Tengyez/bcdwatch/docs/assembled-pcb.png

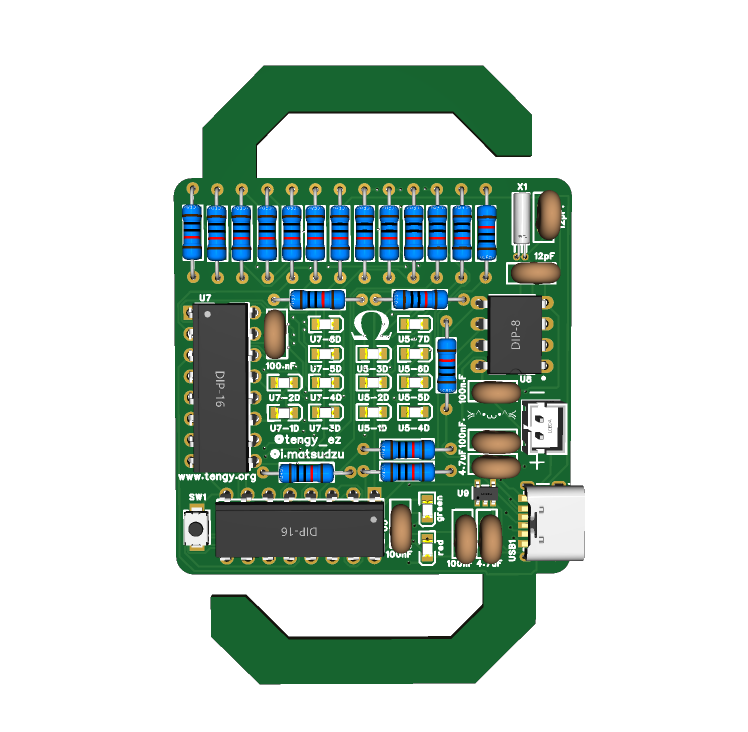
docs/assembled-pcb.png
