Tengyez/bcdwatch/docs/pcb-wiring.png

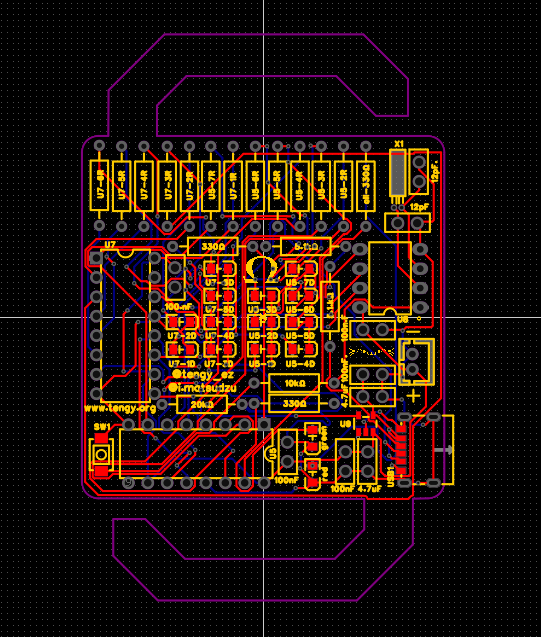
docs/pcb-wiring.png
